AwesomeAudioApparatus/demiurge/photos/demiurge1-kit-1.jpg

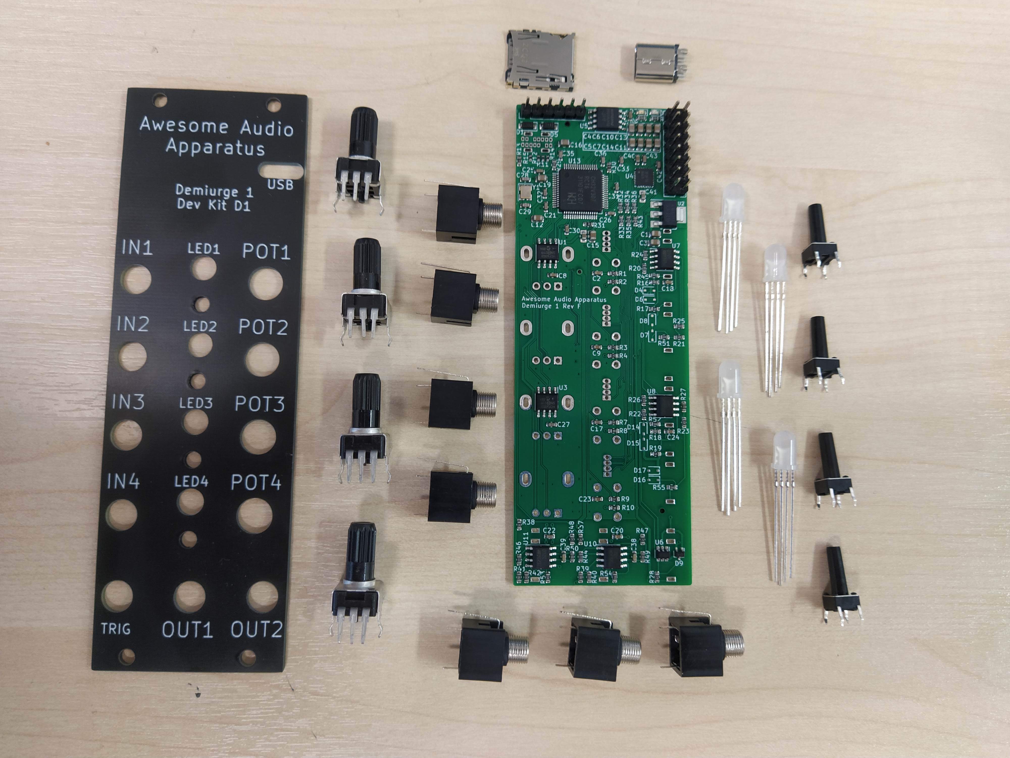
photos/demiurge1-kit-1.jpg
