AwesomeAudioApparatus/demiurge/photos/demiurge1-kit-3.jpg

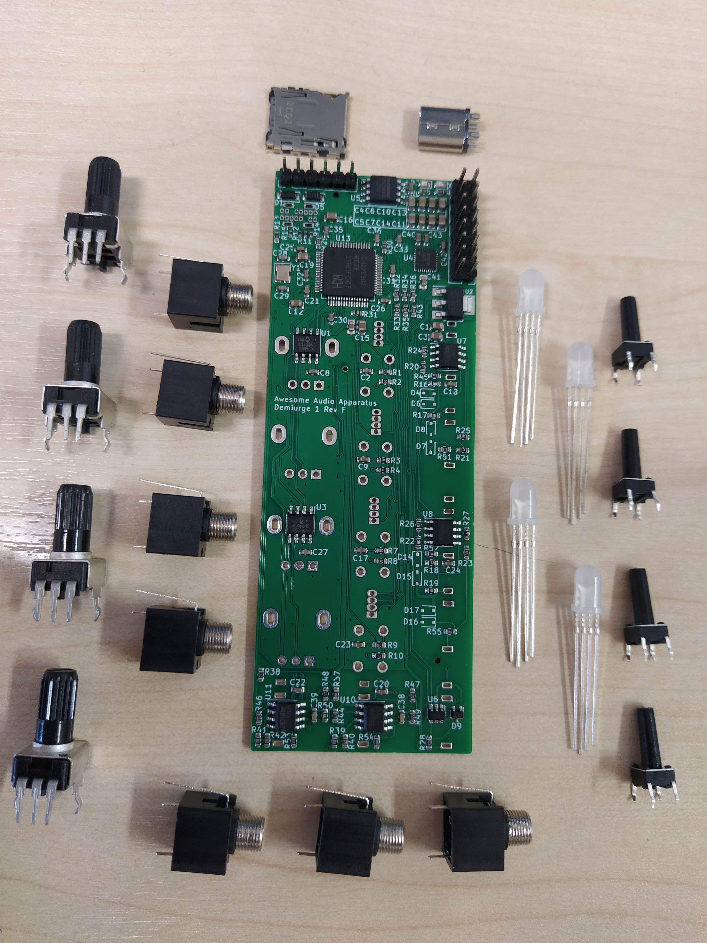
photos/demiurge1-kit-3.jpg
