AwesomeAudioApparatus/demiurge/photos/demiurge1-kit-4.jpg

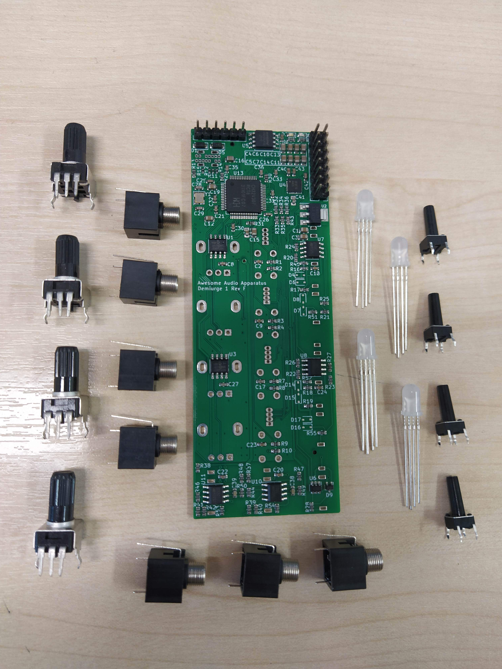
photos/demiurge1-kit-4.jpg
