AwesomeAudioApparatus/demiurge/photos/demiurge1-RevE-1.png

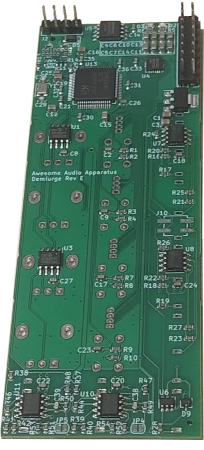
photos/demiurge1-RevE-1.png
