AwesomeAudioApparatus/demiurge/photos/demiurge1-RevE-2.jpg

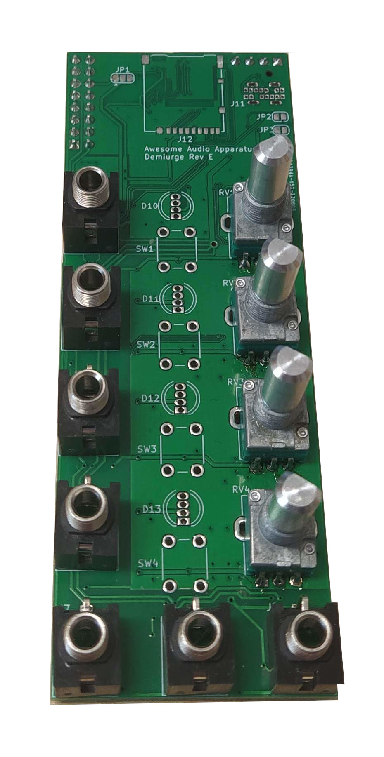
photos/demiurge1-RevE-2.jpg
