AwesomeAudioApparatus/demiurge/photos/demiurge1-RevE-3.jpg

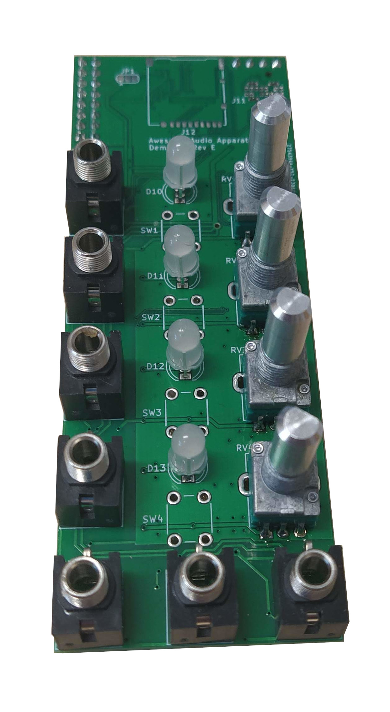
photos/demiurge1-RevE-3.jpg
