AwesomeAudioApparatus/demiurge/photos/demiurge1-RevF-1.jpg

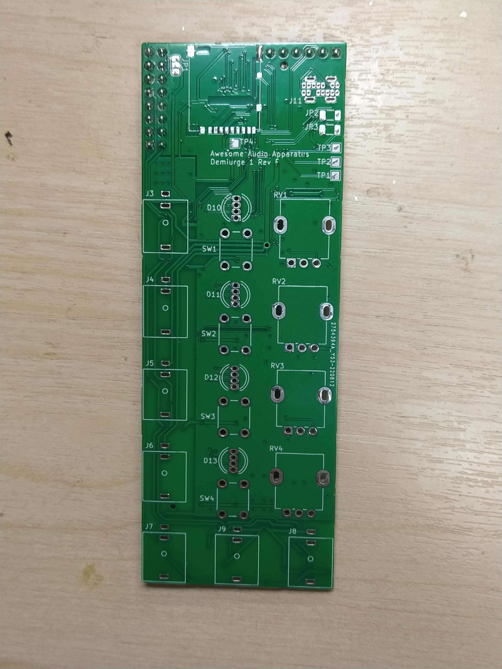
photos/demiurge1-RevF-1.jpg
