AwesomeAudioApparatus/demiurge/photos/demiurge1-RevF-2.jpg

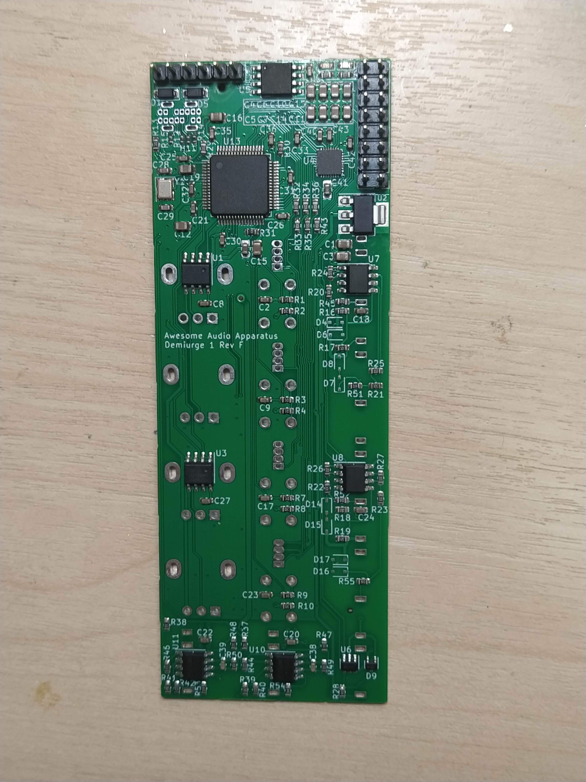
photos/demiurge1-RevF-2.jpg
