AwesomeAudioApparatus/demiurge/photos/demiurge1-RevF-3.jpg

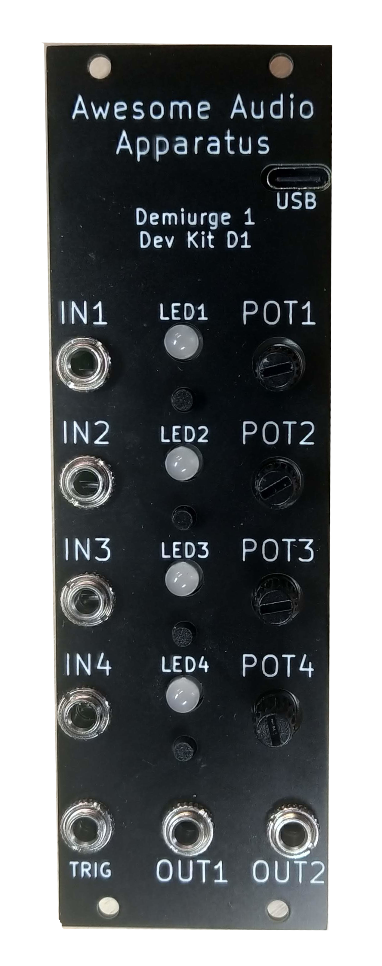
photos/demiurge1-RevF-3.jpg
