AwesomeAudioApparatus/demiurge/photos/demiurge1-RevF-4.jpg

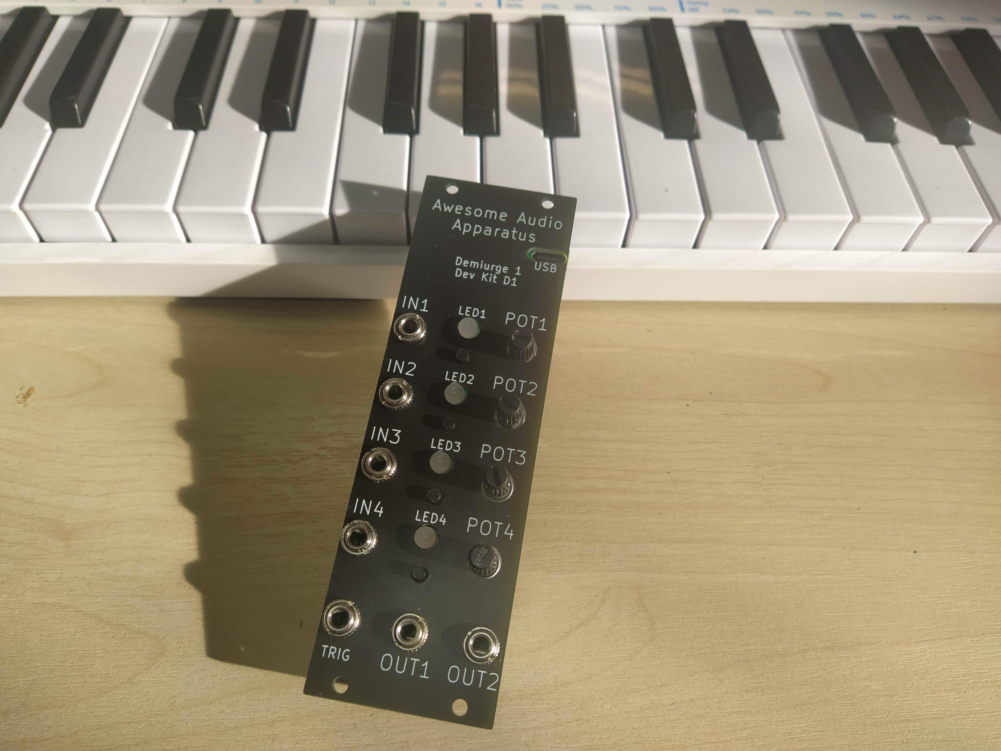
photos/demiurge1-RevF-4.jpg
