AwesomeAudioApparatus/demiurge/photos/demiurge1-RevF-5.jpg

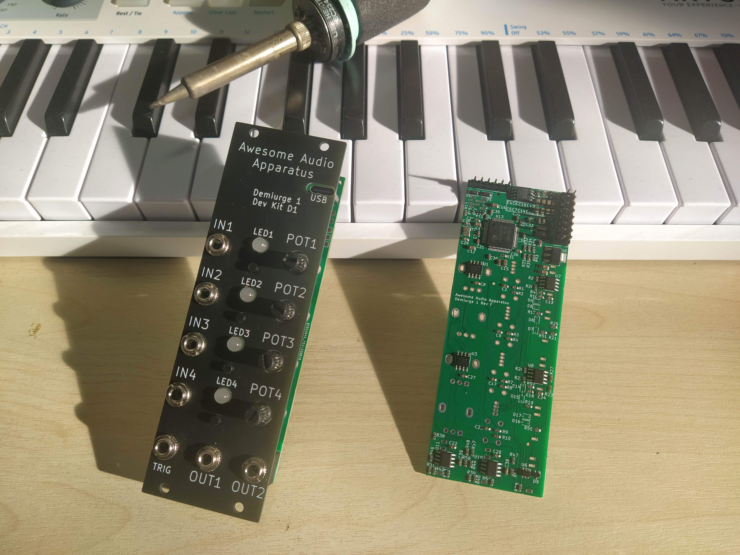
photos/demiurge1-RevF-5.jpg
