AwesomeAudioApparatus/demiurge/photos/demiurge1-RevF-6.jpg

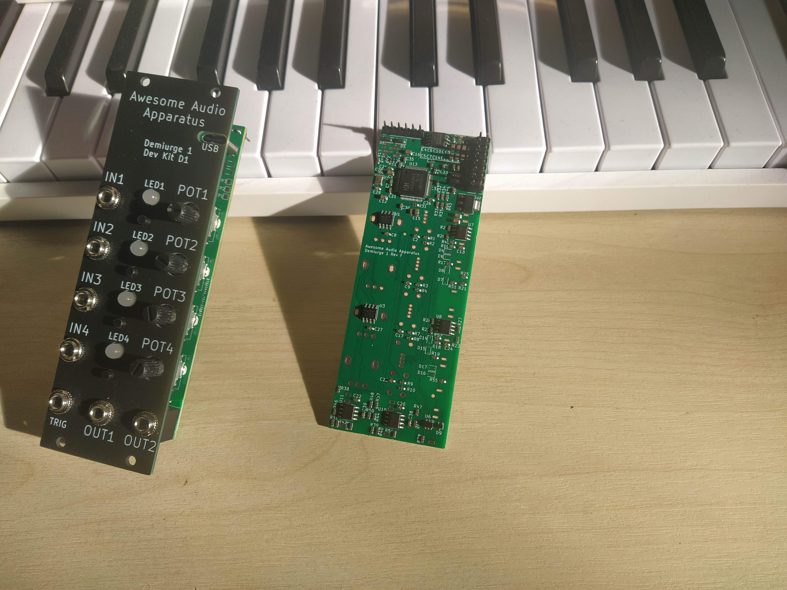
photos/demiurge1-RevF-6.jpg
