AwesomeAudioApparatus/demiurge/photos/demiurge1-RevF-7.jpg

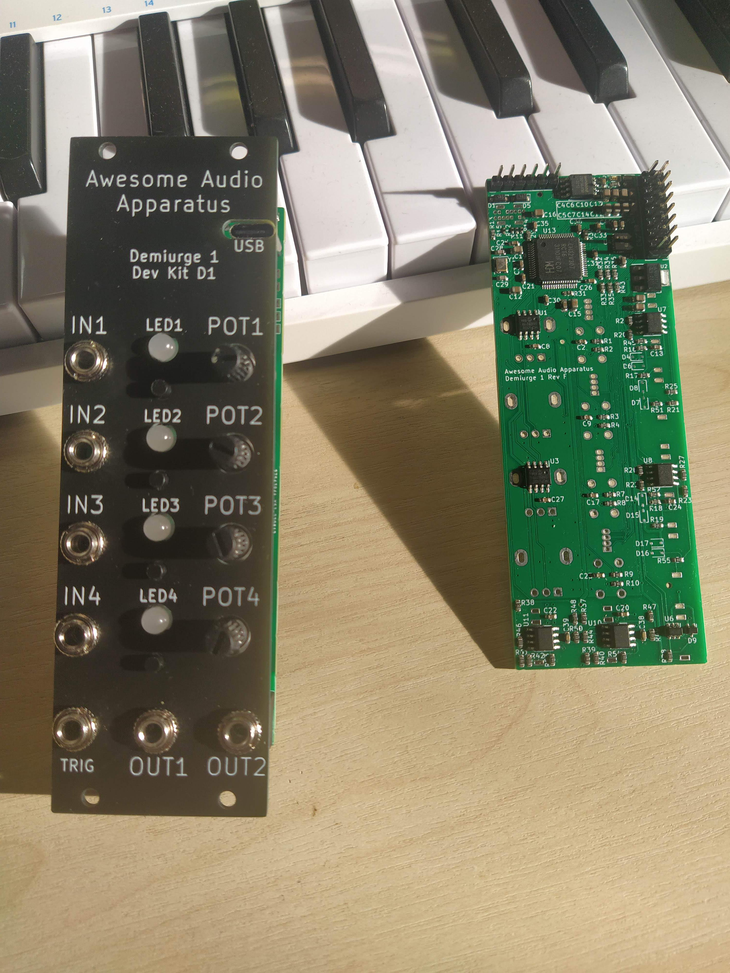
photos/demiurge1-RevF-7.jpg
