AwesomeAudioApparatus/demiurge/photos/demiurge1-RevF-8.jpg

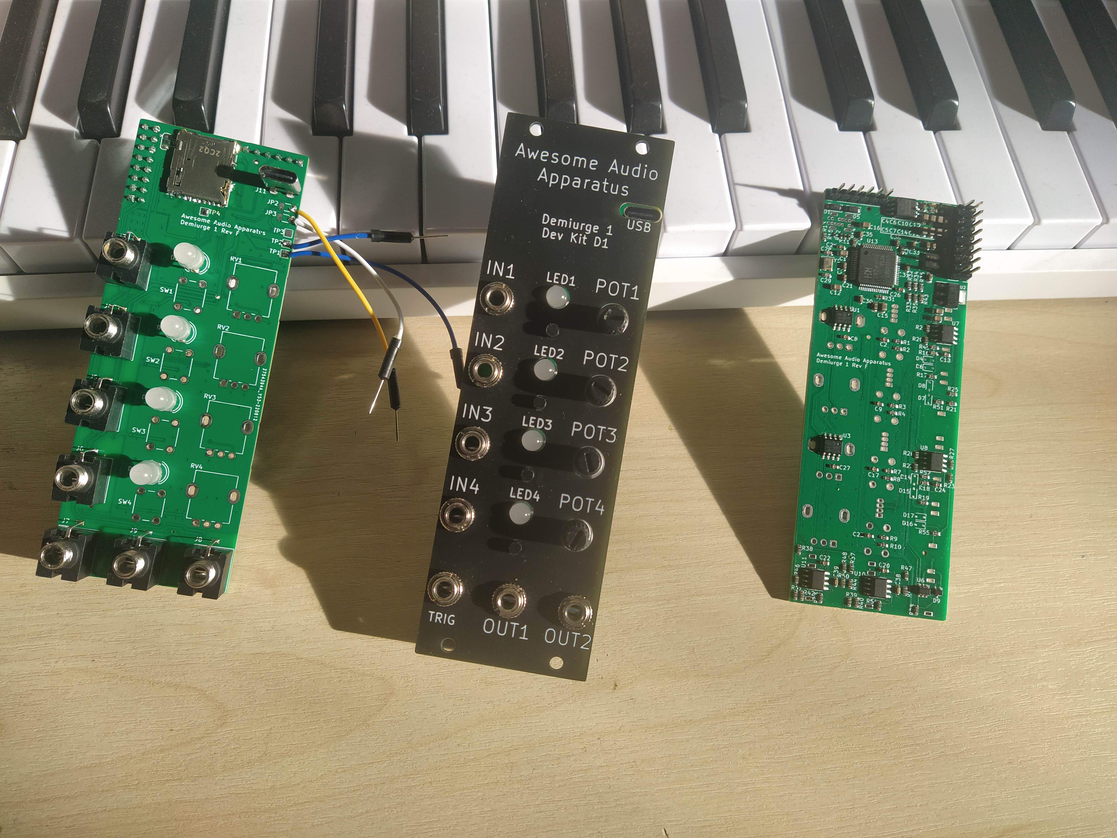
photos/demiurge1-RevF-8.jpg
