AwesomeAudioApparatus/demiurge/photos/demiurge1-RevG-9.jpg

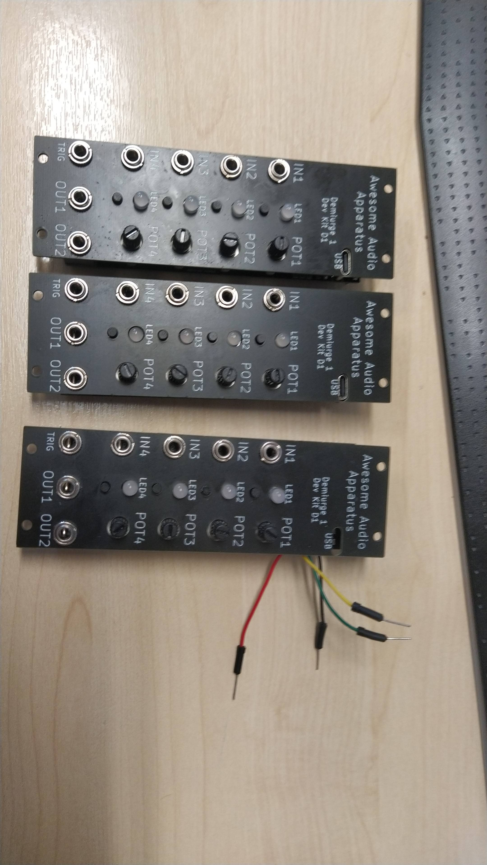
photos/demiurge1-RevG-9.jpg
