AwesomeAudioApparatus/demiurge/photos/demiurge1-RevG-11.jpg

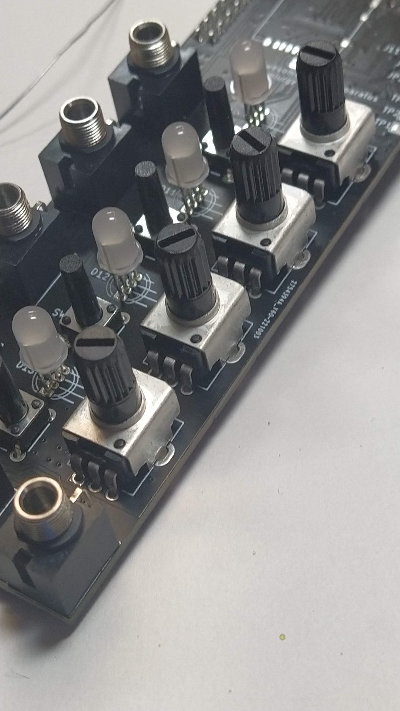
photos/demiurge1-RevG-11.jpg
