AwesomeAudioApparatus/demiurge/photos/demiurge1-RevG-12.jpg

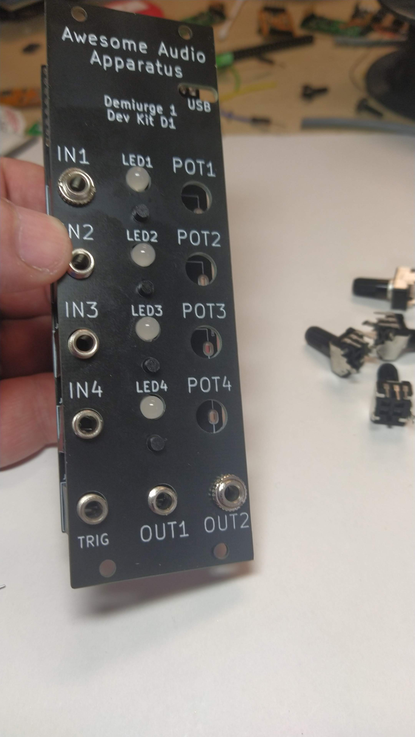
photos/demiurge1-RevG-12.jpg
