AwesomeAudioApparatus/demiurge/photos/demiurge1-RevG-13.jpg

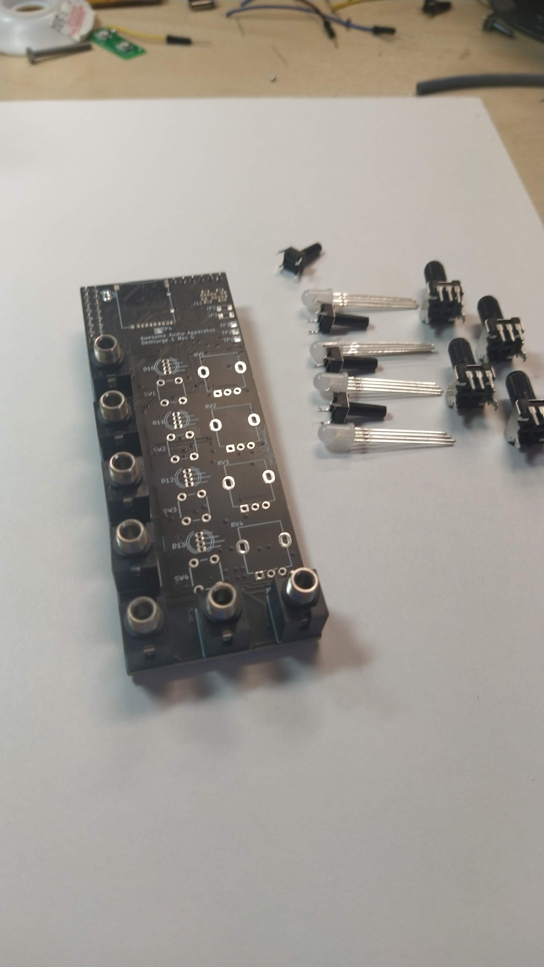
photos/demiurge1-RevG-13.jpg
