AwesomeAudioApparatus/demiurge/photos/knob-1.jpg

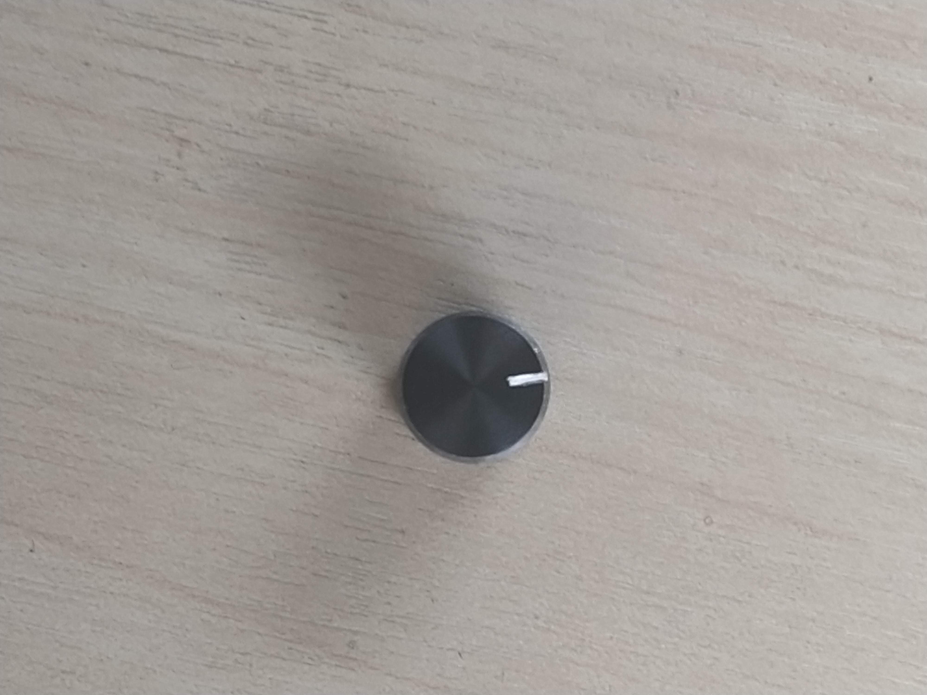
photos/knob-1.jpg
