AwesomeAudioApparatus/demiurge/photos/knob-2.jpg

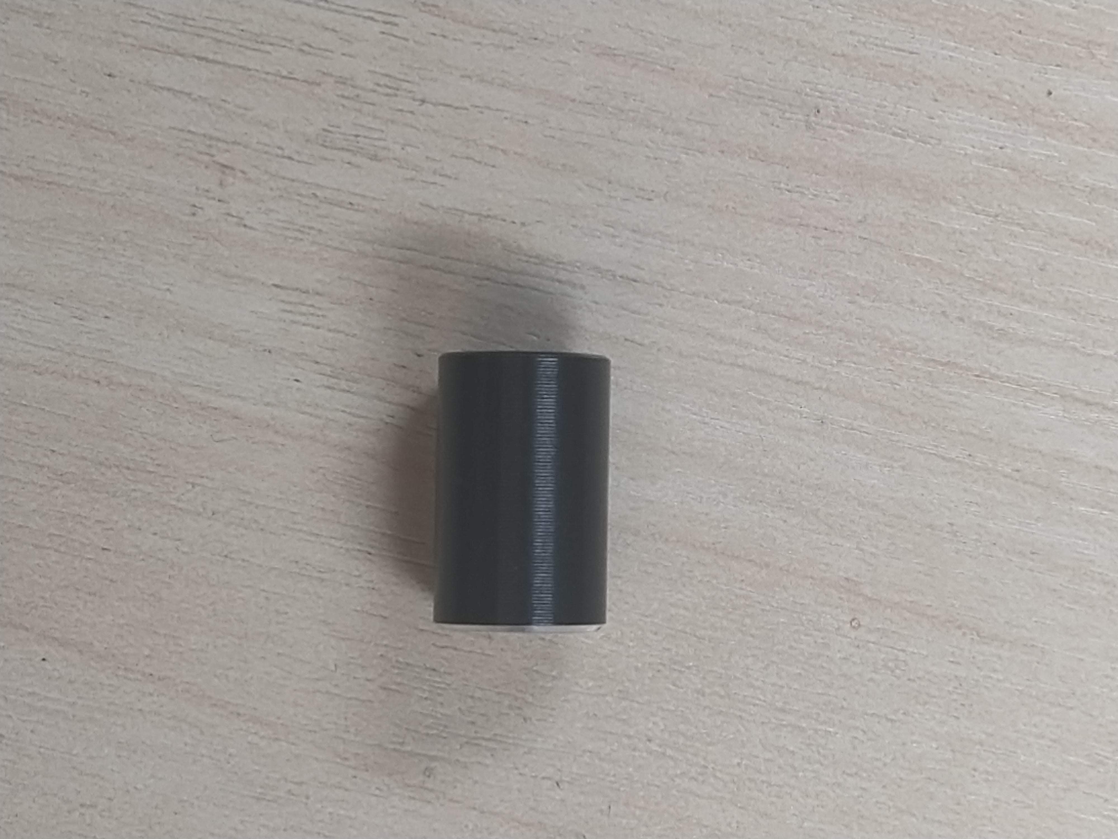
photos/knob-2.jpg
