AwesomeAudioApparatus/demiurge/photos/knob-3.jpg

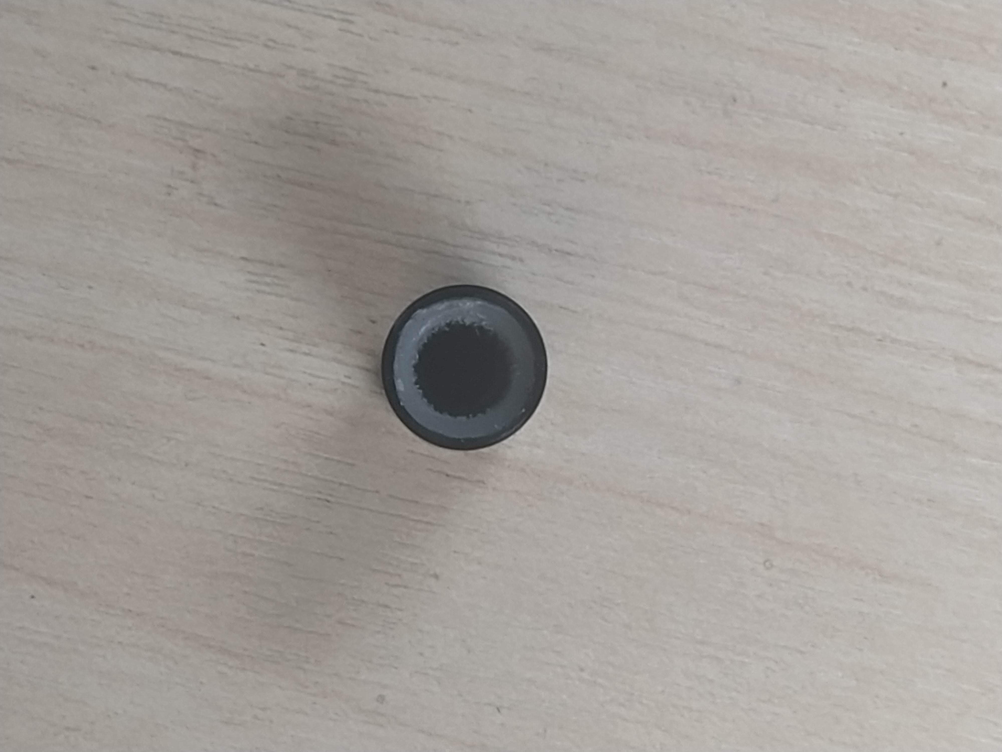
photos/knob-3.jpg
