AwesomeAudioApparatus/demiurge/photos/opencart/knob-4-opencart.jpg

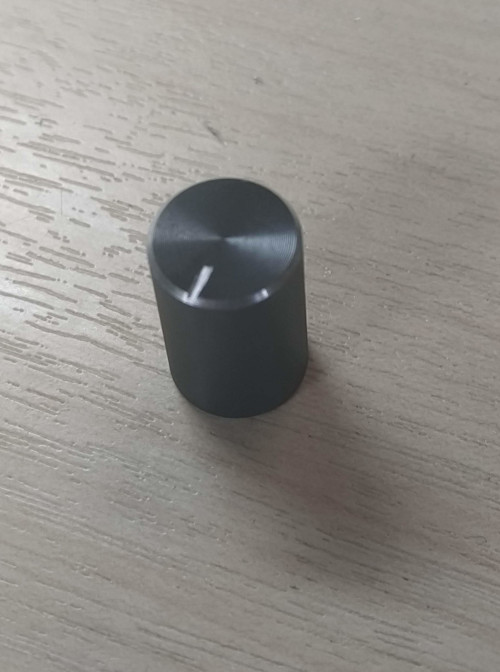
photos/opencart/knob-4-opencart.jpg
