AwesomeAudioApparatus/demiurge/photos/opencart/Knob-RevF-1.jpeg

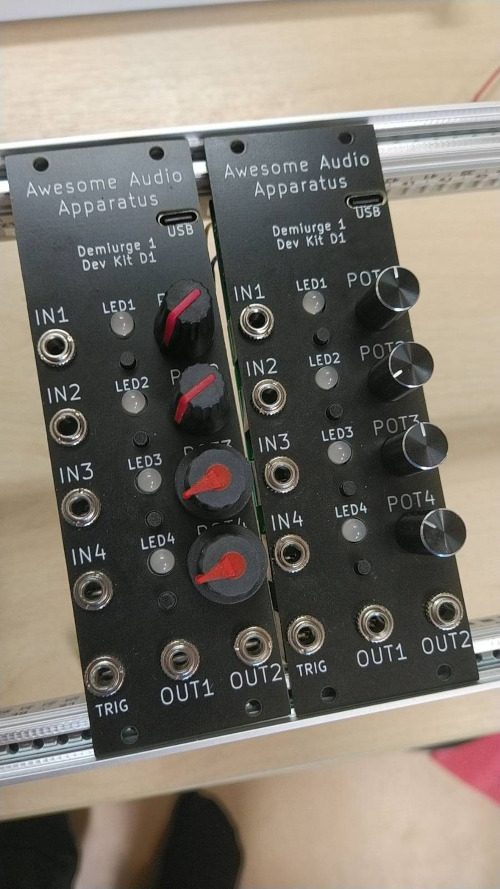
photos/opencart/Knob-RevF-1.jpeg
