AwesomeAudioApparatus/demiurge/wiki-images/Update-STlink2.png

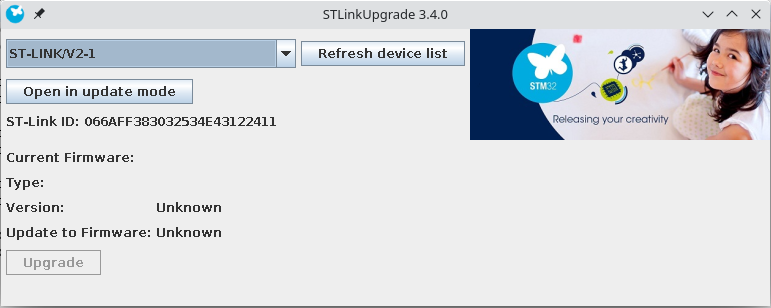
wiki-images/Update-STlink2.png
