AwesomeAudioApparatus/demiurge/wiki-images/Update-STlink3.png

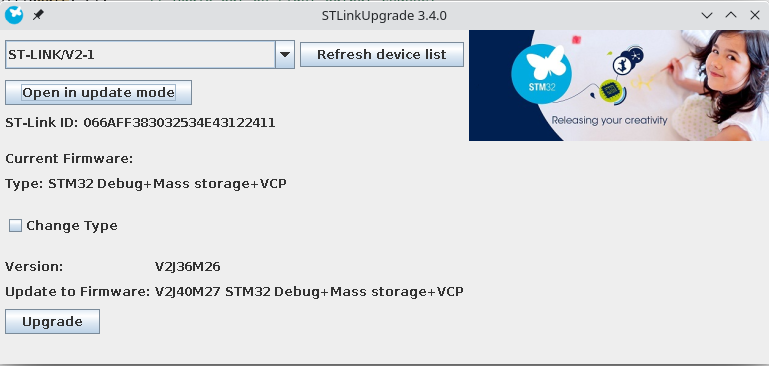
wiki-images/Update-STlink3.png
