AwesomeAudioApparatus/demiurge/wiki-images/Update-STlink.png

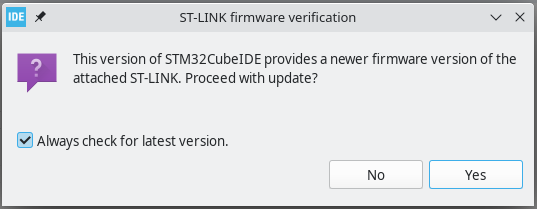
wiki-images/Update-STlink.png
