AwesomeAudioApparatus/demiurge/software/User/AwesomeAudioApparatus.Demiurge_conf.h

/**
  ******************************************************************************
  * File Name          : AwesomeAudioApparatus.Demiurge_conf.h
  * Description        : This file provides code for the configuration
  *                      of the AwesomeAudioApparatus.Demiurge_conf.h instances.
  ******************************************************************************
  * @attention
  *
  * Copyright (c) 2022 STMicroelectronics.
  * All rights reserved.
  *
  * This software is licensed under terms that can be found in the LICENSE file
  * in the root directory of this software component.
  * If no LICENSE file comes with this software, it is provided AS-IS.
  *
  ******************************************************************************
  */
/* Define to prevent recursive inclusion -------------------------------------*/
#ifndef __AWESOMEAUDIOAPPARATUS__DEMIURGE_CONF__H__
#define __AWESOMEAUDIOAPPARATUS__DEMIURGE_CONF__H__

#ifdef __cplusplus
 extern "C" {
#endif

/* Includes ------------------------------------------------------------------*/

/**
	MiddleWare name : AwesomeAudioApparatus.Demiurge.0.2.0
	MiddleWare fileName : ./AwesomeAudioApparatus.Demiurge_conf.h
	MiddleWare version :
*/
/*---------- SAMPLERATE  -----------*/
#define SAMPLERATE      48000

/*---------- TYPE_INPUT1  -----------*/
#define TYPE_INPUT1      CV

/*---------- TYPE_INPUT2  -----------*/
#define TYPE_INPUT2      CV

/*---------- TYPE_INPUT3  -----------*/
#define TYPE_INPUT3      CV

/*---------- TYPE_INPUT4  -----------*/
#define TYPE_INPUT4      CV

/*---------- TYPE_OUTPUT1  -----------*/
#define TYPE_OUTPUT1      CV

/*---------- TYPE_OUTPUT2  -----------*/
#define TYPE_OUTPUT2      CV

#ifdef __cplusplus
}
#endif
#endif /*__AWESOMEAUDIOAPPARATUS__DEMIURGE_CONF__H__ */

/**
  * @}
  */

/************************ (C) COPYRIGHT STMicroelectronics *****END OF FILE****/
